unusual-thoughts/8x8matrix/arduino/nyan_demo.ino

#include "Tlc5947.h"
const uint8_t PROGMEM nyan[(8 * 8 * 3 + 1) * 32] =
	("\0""3f\0""3f\0""3f\0""3f\0""3f\0""3f\0""3f\0""3f\0""3f\0""3f\0""3f\0""3f\0"
	 """3f\0""3f\0""3f\0""3f\0""3f\0""3f\0""3f\0""3f\0""3f\0""3f\0""3f\0""3f\0""3"
	 "f\0""3f\0""3f\0""3f\0""3f\0""3f\0""3f\0""3f\0""3f\0""3f\0""3f\0""3f\0""3f"
	 "\0""3f\0""3f\0""3f\0""3f\0""3f\0""3f\0""3f\0""3f\0""3f\0""3f\0""3f\0""3f\0"
	 """3f\0""3f\0""3f\0""3f\0""3f\0""3f\0""3f\0""3f\0""3f\0""3f\0""3f\0""3f\0""3"
	 "f\0""3f\0""3f"

	 "\0""3f\0""3f\0""3f\0""3f\0""3f\0""3f\0""3f\0""3f\0""3f\0""3f\0""3f\0""3f\0"
	 """3f\0""3f\0""3f\0""3f\0""3f\0""3f\0""3f\0""3f\0""3f\0""3f\0""3f\0""3f\0""3"
	 "f\0""3f\0""3f\0""3f\0""3f\0""3f\0""3f\0""3f\231\231\231\0""3f\0""3f\0""3f"
	 "\0""3f\0""3f\0""3f\0""3f\377\242\240\0""3f\0""3f\0""3f\0""3f\0""3f\0""3f\0"
	 """3f\0""3f\0""3f\0""3f\0""3f\0""3f\0""3f\0""3f\0""3f\0""3f\0""3f\0""3f\0""3"
	 "f\0""3f\0""3f\0""3f\0""3f"

	 "\0""3f\0""3f\0""3f\0""3f\0""3f\0""3f\0""3f\0""3f\0""3f\0""3f\0""3f\0""3f\0"
	 """3f\0""3f\0""3f\0""3f\0""3f\231\231\231\0""3f\0""3f\0""3f\0""3f\0""3f\0""3"
	 "f\231\231\231\231\231\231\0""3f\0""3f\0""3f\0""3f\0""3f\0""3f\231\231\231"
	 "\0\0\0\231\231\231\0""3f\0""3f\0""3f\0""3f\0""3f\231\231\231\231\231\231\377"
	 "\242\240\0""3f\0""3f\0""3f\0""3f\0""3f\231\231\231\231\231\231\0""3f\0""3"
	 "f\0""3f\0""3f\0""3f\0""3f\0""3f\0""3f\0""3f\0""3f\0""3f\0""3f\0""3f\0""3f"

	 "\0""3f\0""3f\0""3f\0""3f\0""3f\0""3f\0""3f\0""3f\0""3f\0""3f\0""3f\0""3f\0"
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
	2937, 2971, 3004, 3038, 3072, 3107, 3141, 3176, 3212, 3247, 3283, 3319, 3355, 3392, 3428, 3465,
	3503, 3540, 3578, 3616, 3654, 3693, 3732, 3771, 3811, 3850, 3890, 3931, 3971, 4012, 4053, 4095
};
//*/
//*
const uint8_t PROGMEM PROGMEM cielab_8bit[] =
{
	0,   0,   0,   0,   0,   0,   0,   0,   0,   1,   1,   1,   1,   1,   1,   1,
	1,   1,   2,   2,   2,   2,   2,   2,   2,   2,   2,   3,   3,   3,   3,   3,
	3,   3,   4,   4,   4,   4,   4,   5,   5,   5,   5,   5,   6,   6,   6,   6,
	6,   7,   7,   7,   7,   8,   8,   8,   8,   9,   9,   9,   10,  10,  10,  11,
	11,  11,  12,  12,  12,  13,  13,  13,  14,  14,  14,  15,  15,  16,  16,  17,
	17,  17,  18,  18,  19,  19,  20,  20,  21,  21,  22,  22,  23,  23,  24,  24,
	25,  25,  26,  27,  27,  28,  28,  29,  30,  30,  31,  31,  32,  33,  33,  34,
	35,  35,  36,  37,  38,  38,  39,  40,  41,  41,  42,  43,  44,  45,  45,  46,
	47,  48,  49,  50,  51,  51,  52,  53,  54,  55,  56,  57,  58,  59,  60,  61,
	62,  63,  64,  65,  66,  67,  68,  69,  70,  71,  73,  74,  75,  76,  77,  78,
	80,  81,  82,  83,  84,  86,  87,  88,  90,  91,  92,  93,  95,  96,  98,  99,
	100, 102, 103, 105, 106, 107, 109, 110, 112, 113, 115, 116, 118, 120, 121, 123,
	124, 126, 128, 129, 131, 132, 134, 136, 138, 139, 141, 143, 145, 146, 148, 150,
	152, 154, 155, 157, 159, 161, 163, 165, 167, 169, 171, 173, 175, 177, 179, 181,
	183, 185, 187, 189, 192, 194, 196, 198, 200, 202, 205, 207, 209, 212, 214, 216,
	218, 221, 223, 226, 228, 230, 233, 235, 238, 240, 243, 245, 248, 250, 253, 255
};
//*/

int gammapow(int i)
{
	return int(pow(float(i) / 256, 2.2) * 4095);
}

void setup()
{
	Tlc.init(0);
	Serial.begin(9600);
}

uint16_t i = 0;
int a = 0;

char serial_vect[256];
uint8_t serial_count = 0;
uint16_t pos;
char text[256] = "   On peut faire defiler du texte de TOUTES LES COULEURS!!! Youpi c'est trop genial! henritonchain@gmail.com";
uint16_t len = text_width(text);

void loop()
{
	//scroll_text_smooth(10, 20);
	for (i = 0; i < 5; i++)
	{
		animation(nyan, 70, 32);
		delay_serial(500);
	}

	scroll_text();

	delay_serial(1000);
	fadePict(creeper);
	delay_serial(1000);
	fadePict(bonhomme);
	delay_serial(1000);

	for (i = 0; i < 48; i++)
	{
		Tlc.shiftRight();
		delay_serial(100);
	}

	//Tlc.clear();
	for (i = 0; i < 800; i++)
	{
		snow();
		delay_serial(20);
	}

	for (int a = 0; a < 256; a++)
	{
		circular_sine(a);
		delay_serial(50);
	}

	fadePict(pig);
	delay_serial(1000);
	fadePict(maison);
	delay_serial(1000);
	fadePict(arcenciel);
	delay_serial(1000);
	fadePict(jojo);
	delay_serial(1000);
	fadePict(zombie);
	delay_serial(1000);


}

uint16_t text_width(char *str)
{
	uint16_t len = 0;
	while (*str)
	{
		if (*str >= 32 && *str <= 126) // is printable
			len += pgm_read_byte(&font_width[(*str) - 32]);
		str++;
		len++;
	}
	return (len);
}


void show_text(char *str, uint16_t pos, uint16_t r, uint16_t g, uint16_t b)
{
	uint16_t sum = 0, oldsum = 0;
	uint8_t i, x, y;
	i = 0;
	while (str[i] && sum <= pos) // < or <= ??
	{
		oldsum = sum;
		if (str[i] >= 32 && str[i] <= 126) // is printable
			sum += pgm_read_byte(&font_width[(str[i]) - 32]);
		i++;
		sum++;
	}
	if (i > 0) i--;
	for (x = pos - oldsum; x < pgm_read_byte(&font_width[(str[i]) - 32]); x++)
	{
		for (y = 0; y < 8; y++)
		{
			if (str[i] >= 32 && str[i] <= 126)
				if (pgm_read_byte(&font[(str[i] - 32) * 8 + y]) & (1 << x))
					Tlc.setLED(7 - y, x - pos + oldsum, r, g, b);
		}
	}
	i++;
	while (str[i] && sum < pos + 8)
	{
		for (x = 0 ; x < pgm_read_byte(&font_width[(str[i]) - 32]) && x - pos + sum < 8; x++)
		{
			for (y = 0; y < 8; y++)
			{
				if (str[i] >= 32 && str[i] <= 126)
					if (pgm_read_byte(&font[(str[i] - 32) * 8 + y]) & (1 << x))
						Tlc.setLED(7 - y, x - pos + sum, r, g, b);
			}
			//x++;
			//sum++;
		}
		sum += pgm_read_byte(&font_width[(str[i]) - 32]);
		sum++;
		i++;
	}
}

void scroll_text()
{
	for (pos = 0; pos < len; pos++)
	{
		Tlc.clear();
		switch ((pos * 6) / len)
		{
		case 0:
			show_text(text, pos, 4095, pgm_read_word(&cielab_12bit[(((pos % (len / 6)) * 255) / (len / 6))]), 0);
			break;
		case 1:
			show_text(text, pos,  pgm_read_word(&cielab_12bit[255 - (((pos % (len / 6)) * 255) / (len / 6))]), 4095, 0);
			break;
		case 2:
			show_text(text, pos,	0, 4095, pgm_read_word(&cielab_12bit[(((pos % (len / 6)) * 255) / (len / 6))]));
			break;
		case 3:
			show_text(text, pos, 0, pgm_read_word(&cielab_12bit[255 - (((pos % (len / 6)) * 255) / (len / 6))]), 4095);
			break;
		case 4:
			show_text(text, pos, pgm_read_word(&cielab_12bit[(((pos % (len / 6)) * 255) / (len / 6))]), 0, 4095);
			break;
		case 5:
			show_text(text, pos, 4095, 0, pgm_read_word(&cielab_12bit[255 - (((pos % (len / 6)) * 255) / (len / 6))]));
			break;
		}
		delay_serial(70);
	}
}

void scroll_text_smooth(uint8_t steps, uint8_t delta)
{
	uint8_t step;
	for (pos = 0; pos < len; pos++)
	{
		for(step = 0 ; step < steps / 2; step++)
		{
			Tlc.clear();
			show_text(text, pos, pgm_read_word(&cielab_12bit[step * (255 / steps)]), pgm_read_word(&cielab_12bit[step * (255 / steps)]), pgm_read_word(&cielab_12bit[step * (255 / steps)]));
			show_text(text, pos - 1, pgm_read_word(&cielab_12bit[(steps - step) * (255 / steps)]), pgm_read_word(&cielab_12bit[(steps - step) * (255 / steps)]), pgm_read_word(&cielab_12bit[(steps - step) * (255 / steps)]));
			delay_serial(delta);
		}
		for(step = steps / 2; step < steps; step++)
		{
			Tlc.clear();
			show_text(text, pos - 1, pgm_read_word(&cielab_12bit[(steps - step) * (255 / steps)]), pgm_read_word(&cielab_12bit[(steps - step) * (255 / steps)]), pgm_read_word(&cielab_12bit[(steps - step) * (255 / steps)]));
			show_text(text, pos, pgm_read_word(&cielab_12bit[step * (255 / steps)]), pgm_read_word(&cielab_12bit[step * (255 / steps)]), pgm_read_word(&cielab_12bit[step * (255 / steps)]));
			delay_serial(delta);
		}
	}
}

void delay_serial(uint16_t howlong)
{
	uint8_t testbyte;
	uint16_t divided = howlong;
	uint16_t i;
	for (i = 0; i < divided; i++)
	{

		while (Serial.available() > 0)
		{
			// read the incoming byte:
			serial_vect[serial_count] = Serial.read();
			//testbyte = Serial.read();
			// say what you got:
			//Serial.print("I received: ");
			//Serial.println(serial_vect[serial_count], DEC);
			//Serial.println(testbyte, DEC);
			if (serial_vect[serial_count] == '\n')
			{
				if (serial_count == 12)
				{
					Serial.println("set color");
					Tlc.setAllLED((serial_vect[0] - '0') * 1000 + (serial_vect[1] - '0') * 100 + (serial_vect[2] - '0') * 10 + serial_vect[3] - '0',
								  (serial_vect[4] - '0') * 1000 + (serial_vect[5] - '0') * 100 + (serial_vect[6] - '0') * 10 + serial_vect[7] - '0',
								  (serial_vect[8] - '0') * 1000 + (serial_vect[9] - '0') * 100 + (serial_vect[10] - '0') * 10 + serial_vect[11] - '0');
					delay_serial(1000);
				}
				else
				{
					Serial.println("set text");
					pos = 0;
					serial_vect[serial_count] = 0;
					strcpy(text, serial_vect);
					len = text_width(text);
				}
				serial_count = -1;
			}

			serial_count++;
			serial_count %= 256;

		}

		delay(1);
	}

}
void snow()
{
	int col, row;
	int previous;
	for (col = 7; col >= 0 ; col--)
	{
		for (row = 0; row < 8; row++)
		{
			if (Tlc.get(col, row) == 4095 && random(10) == 0) //only looks at red channel (lednum = col)
			{
				if (col != 0)
					Tlc.setLED(col - 1, row, 4095, 4095, 4095);
				Tlc.setLED(col, row, 0, 0, 0);
			}
		}
	}
	for (row = 0; row < 8; row++)
	{
		if (random(100) == 0)
			Tlc.setLED(7, row, 4095, 4095, 4095);
	}

}

void sine(int a)
{
	int c;
	int r;
	for (c = 0; c < 8; c++)
	{
		for (r = 0; r < 8; r++)
		{
			Tlc.setLED(c, r, pgm_read_word(&cielab_12bit[(int) (127 * (sin(3.14 * (8 * c - 2 * a) / 32) + 1))]),
					   pgm_read_word(&cielab_12bit[(int) (127 * (sin(3.14 * (8 * r - 2 * a) / 32) + 1))]),
					   pgm_read_word(&cielab_12bit[(int) (127 * (sin(3.14 * (8 * (17 - r - c) - 2 * a) / 32) + 1))]));
		}
	}
}

void circular_sine(int a)
{
	int c;
	int r;
	for (c = 0; c < 8; c++)
	{
		for (r = 0; r < 8; r++)
		{
			Tlc.setLED(c, r, pgm_read_word(&cielab_12bit[(int) (127 * (sin(3.14 * (8 * (c * c + r * r) - 8 * a) / 256) + 1))]),
					   pgm_read_word(&cielab_12bit[(int) (127 * (cos(3.14 * (8 * (( 7 - c) * ( 7 - c) + (7 - r) * (7 - r)) - 8 * a) / 256) + 1))]),
					   pgm_read_word(&cielab_12bit[(int) (127 * (cos(3.14 * (8 * ((c) * (c) + (7 - r) * (7 - r)) - 8 * a) / 256) + 1))]));
		}
	}
}

void animation(const uint8_t *pict, uint8_t delta, uint8_t frames)
{
	int a = 1;
	int order = 1;
	for (uint8_t a = 0; a < frames; a++)
	{
		for (uint8_t c = 0; c < 8; c++)
		{
			for (uint8_t r = 0; r < 8; r++)
			{
				Tlc.setLED(r, c, pgm_read_word(&cielab_12bit[pgm_read_byte(&pict[(8 * 8 * 3 ) * a + (c + (7 - r) * 8 ) * 3])]),
						   pgm_read_word(&cielab_12bit[pgm_read_byte(&pict[(8 * 8 * 3 ) * a + (c + (7 - r) * 8 ) * 3 + 1])]),
						   pgm_read_word(&cielab_12bit[pgm_read_byte(&pict[(8 * 8 * 3 ) * a + (c + (7 - r) * 8 ) * 3 + 2])]));
			}
		}
		delay_serial(delta);
	}
}

void fadePict(const uint8_t *pict)
{
	int a = 1;
	int order = 1;
	//while (a != 0)
	//{
	for (int c = 0; c < 8; c++)
	{
		for (int r = 0; r < 8; r++)
		{
			Tlc.setLED(r, c, pgm_read_word(&cielab_12bit[pgm_read_byte(&pict[(c + (7 - r) * 8 ) * 3])]),
					   pgm_read_word(&cielab_12bit[pgm_read_byte(&pict[(c + (7 - r) * 8 ) * 3 + 1])]),
					   pgm_read_word(&cielab_12bit[pgm_read_byte(&pict[(c + (7 - r) * 8 ) * 3 + 2])]));
			//Tlc.setLED(r,4095,
			//4095,
			//4095);
			//Tlc.setLED(r, pict[(c + (7 - r) * 8 )* 3] * 16,
			//			  pict[(c + (7 - r) * 8 )* 3 + 1] * 16,
			//			  pict[(c + (7 - r) * 8 )* 3 + 2] * 16);
		}
		//Tlc.update(c);
		//setColumn(c);
		//Tlc.setRow(c);
	}
	// a += order;
	//if (a == 512) order = -order;
	//}
}
//*/
/*
int channel = 0;
int direction = 1;
void loop()
{
	Tlc.clear();
	//Tlc.set(channel, 1000);
	Tlc.setLED(channel, 1000, 1000, 1000);
		Tlc.update();

	channel += direction;
	if (channel == 8 ) {
	  channel = 0;
	}


	delay_serial(500);

}
*/
